nborkowetz/STM32WL_LoRaSensorNodeDemo/Firmware/Core/Inc/app_config.h

#ifndef SENSOR_NODE_APP_CONFIG_H
#define SENSOR_NODE_APP_CONFIG_H

#include <stdbool.h>

/* All application timing values use milliseconds unless explicitly stated. */
#define APP_ACQUISITION_PERIOD_MS       (10UL * 1000UL)
#define APP_SENSOR_WARMUP_MS            (1000UL)

#define APP_ADC_CHANNEL_COUNT           (4U)
#define APP_ADC_SAMPLE_RATE_HZ          (2000UL) /* Per channel. */
#define APP_ACQUISITION_DURATION_MS     (1000UL)
#define APP_ADC_DMA_BUFFER_SAMPLES      (512U)
#define APP_ADC_DMA_HALF_SAMPLES        (APP_ADC_DMA_BUFFER_SAMPLES / 2U)
#define APP_ACQUISITION_TOTAL_SAMPLES   \
  ((APP_ADC_SAMPLE_RATE_HZ * APP_ADC_CHANNEL_COUNT * APP_ACQUISITION_DURATION_MS) / 1000UL)

#define APP_LORAWAN_PORT                (10U)
#define APP_LORAWAN_CONFIRMED           (false)
#define APP_TX_PAYLOAD_MAX_SIZE         (51U)
#define APP_TELEMETRY_BATCH_COUNT       (6U)
#define APP_TELEMETRY_HEADER_SIZE       (6U)
#define APP_TELEMETRY_MEAN_BITS         (10U)
#define APP_TELEMETRY_VARIANCE_BITS     (4U)
#define APP_TELEMETRY_PAYLOAD_SIZE      \
  (APP_TELEMETRY_HEADER_SIZE + \
   ((APP_TELEMETRY_BATCH_COUNT * APP_ADC_CHANNEL_COUNT * \
     (APP_TELEMETRY_MEAN_BITS + APP_TELEMETRY_VARIANCE_BITS) + 7U) / 8U))

#if ((APP_ADC_DMA_BUFFER_SAMPLES % 2U) != 0U)
#error "APP_ADC_DMA_BUFFER_SAMPLES must be even"
#endif

#if ((APP_ADC_DMA_HALF_SAMPLES % APP_ADC_CHANNEL_COUNT) != 0U)
#error "Each DMA half-buffer must contain complete ADC scan sequences"
#endif

#if ((APP_ACQUISITION_TOTAL_SAMPLES % APP_ADC_CHANNEL_COUNT) != 0U)
#error "APP_ACQUISITION_TOTAL_SAMPLES must contain complete ADC scan sequences"
#endif

#if ((APP_TELEMETRY_MEAN_BITS != 10U) || (APP_TELEMETRY_VARIANCE_BITS != 4U))
#error "Telemetry serializer currently requires 10-bit means and 4-bit variances"
#endif

#if (APP_TX_PAYLOAD_MAX_SIZE < APP_TELEMETRY_PAYLOAD_SIZE)
#error "APP_TX_PAYLOAD_MAX_SIZE is too small for one telemetry record"
#endif

#endif /* SENSOR_NODE_APP_CONFIG_H */
